davidphilipbarr/Sweep/gallery/sweep-bling-lp/back.png

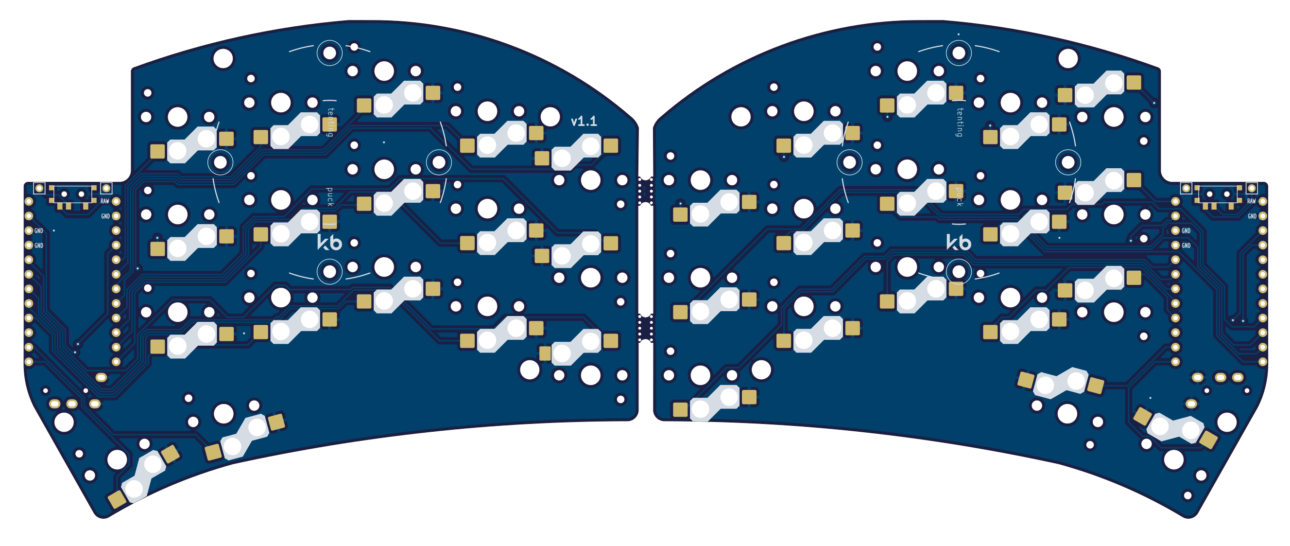
gallery/sweep-bling-lp/back.png
