davidphilipbarr/Sweep/gallery/sweep-bling-lp/front.png

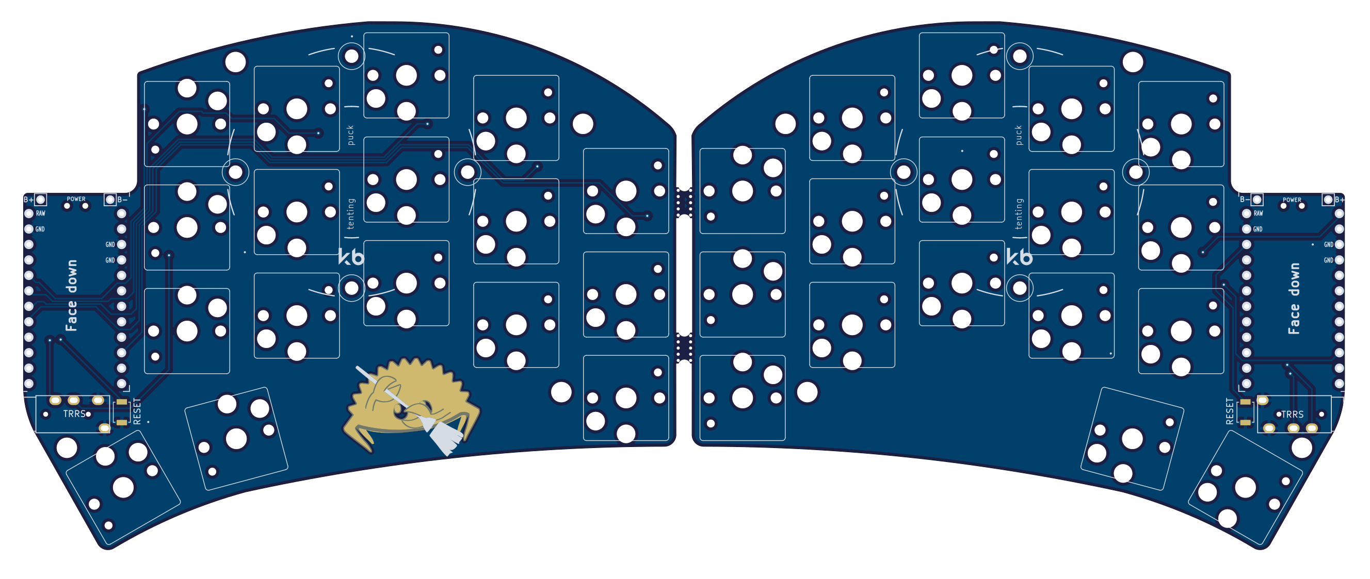
gallery/sweep-bling-lp/front.png
